brodricyoung/mini-crane-project/Documentation/images/schematics/pinout-L298N-B.png

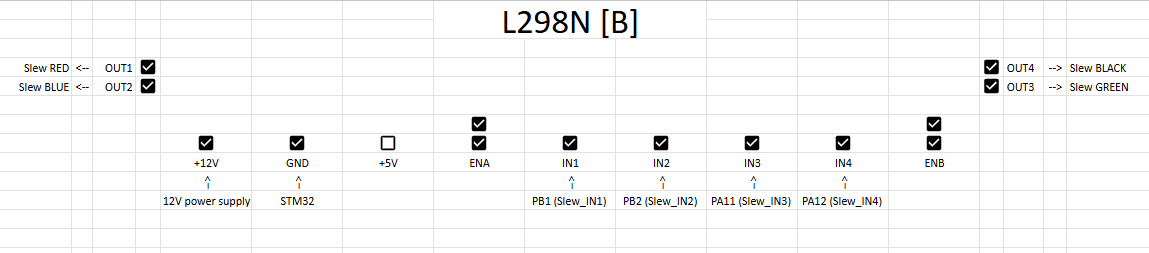
Documentation/images/schematics/pinout-L298N-B.png
