brodricyoung/mini-crane-project/KiCad_files_for_PCB/projects/STM32Nucleo_L476RG_Baseboard/image-of-3d-front-in-KiCad.png

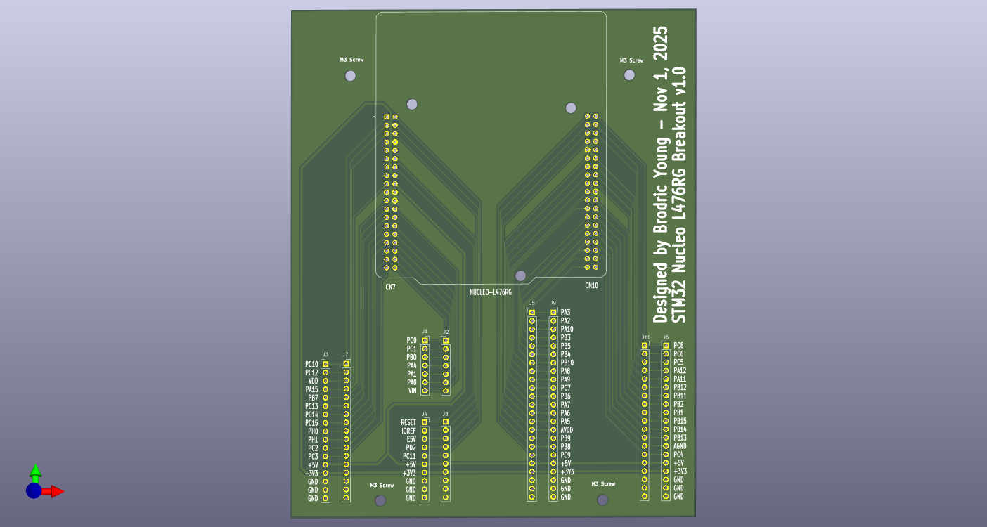
KiCad_files_for_PCB/projects/STM32Nucleo_L476RG_Baseboard/image-of-3d-front-in-KiCad.png
