brodricyoung/mini-crane-project/Documentation/images/components-in-system/pushbuttons-on-controller.JPG

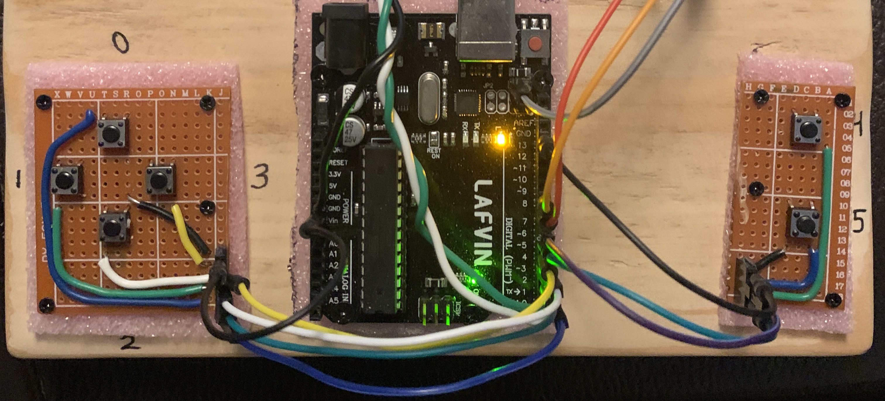
Documentation/images/components-in-system/pushbuttons-on-controller.JPG
