brodricyoung/mini-crane-project/Documentation/images/components-in-system/slew-nema17-stepper-motor.JPG

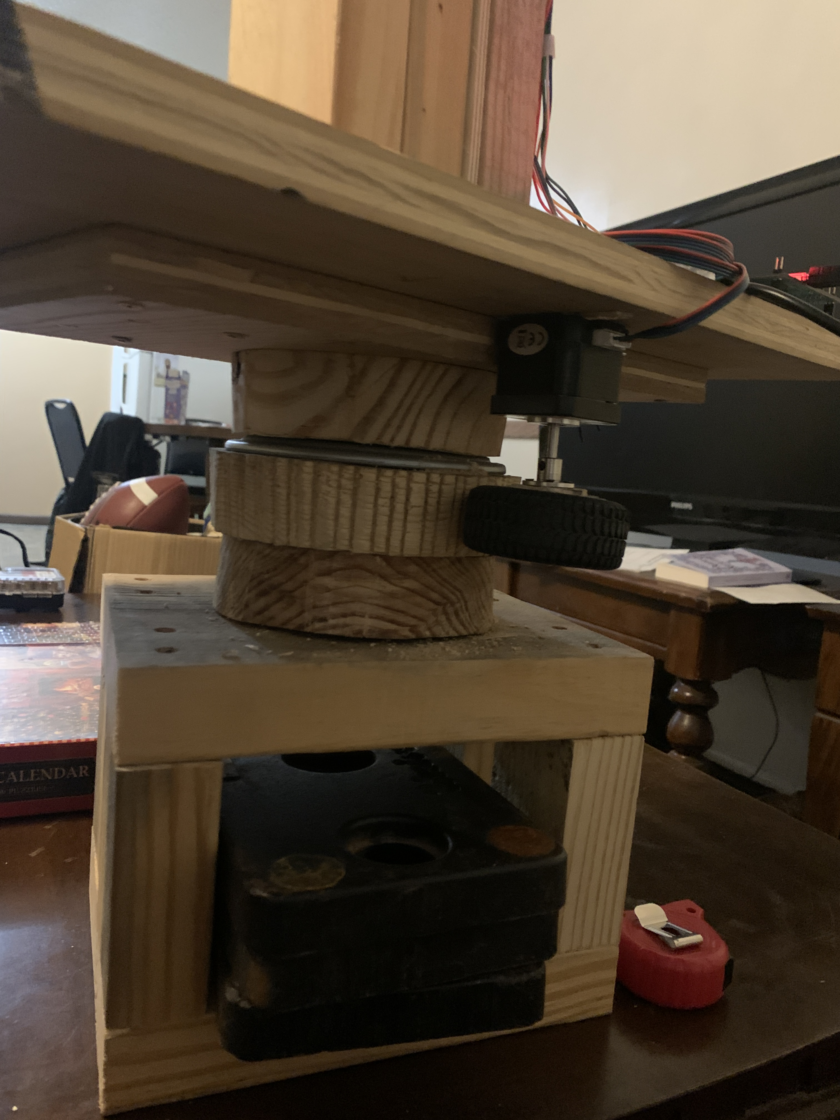
Documentation/images/components-in-system/slew-nema17-stepper-motor.JPG
