brodricyoung/mini-crane-project/Documentation/images/components-in-system/handheld-arduino-controller.JPG

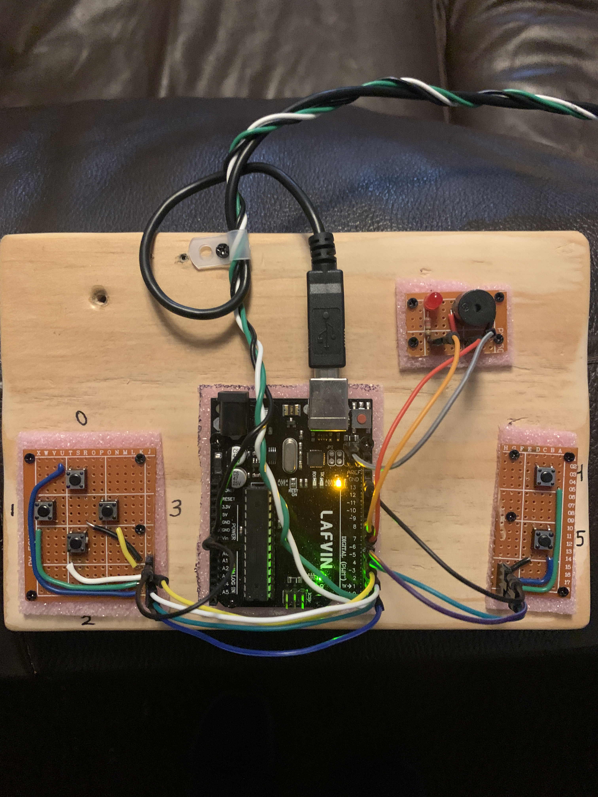
Documentation/images/components-in-system/handheld-arduino-controller.JPG
