brodricyoung/mini-crane-project/Documentation/images/components-in-system/L298N motor drivers.JPG

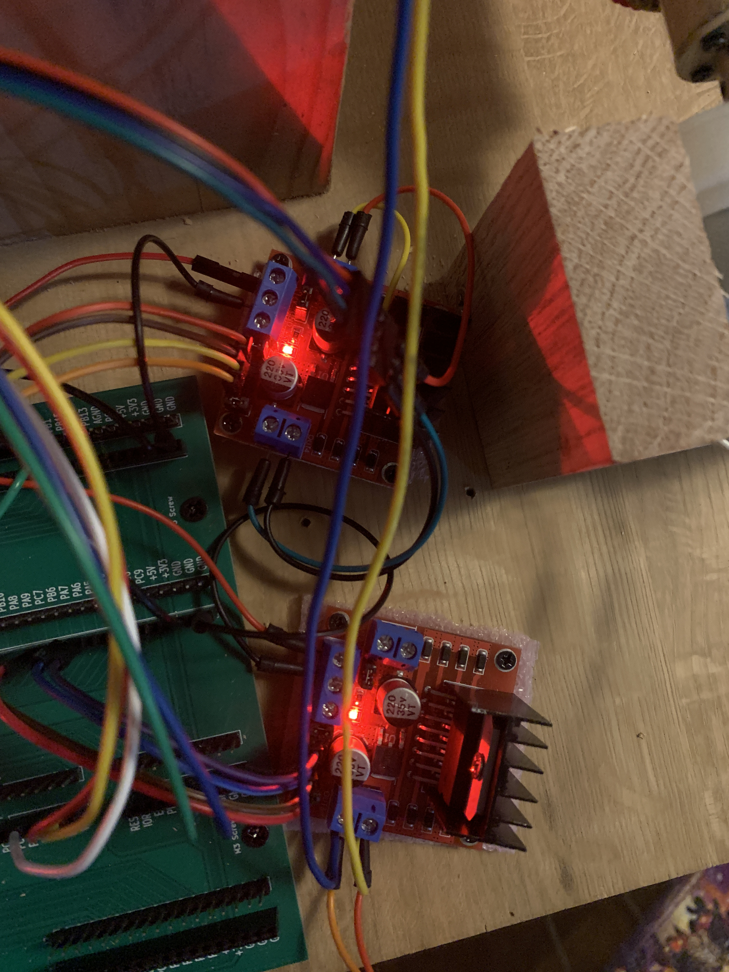
Documentation/images/components-in-system/L298N motor drivers.JPG
