brodricyoung/mini-crane-project/Documentation/images/components-in-system/rotary-encoder.JPG

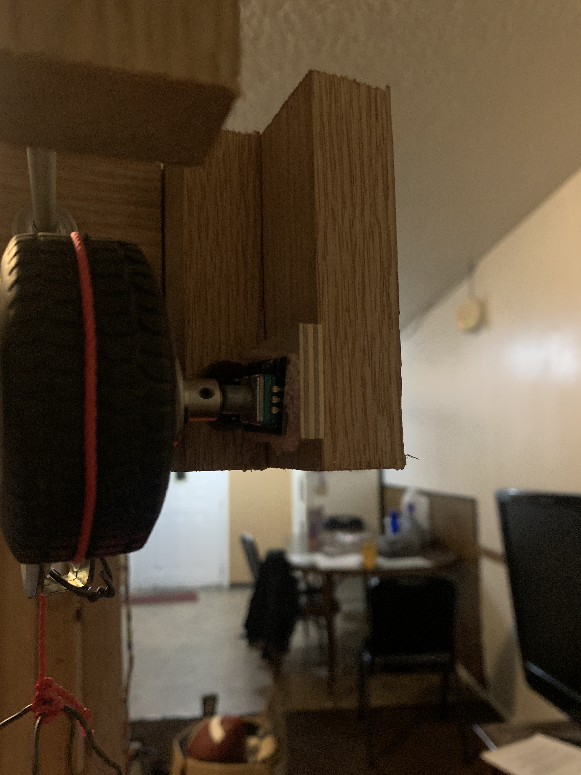
Documentation/images/components-in-system/rotary-encoder.JPG
