brodricyoung/mini-crane-project/Documentation/images/components-in-system/trolley-dc-motor-and-pulley.JPG

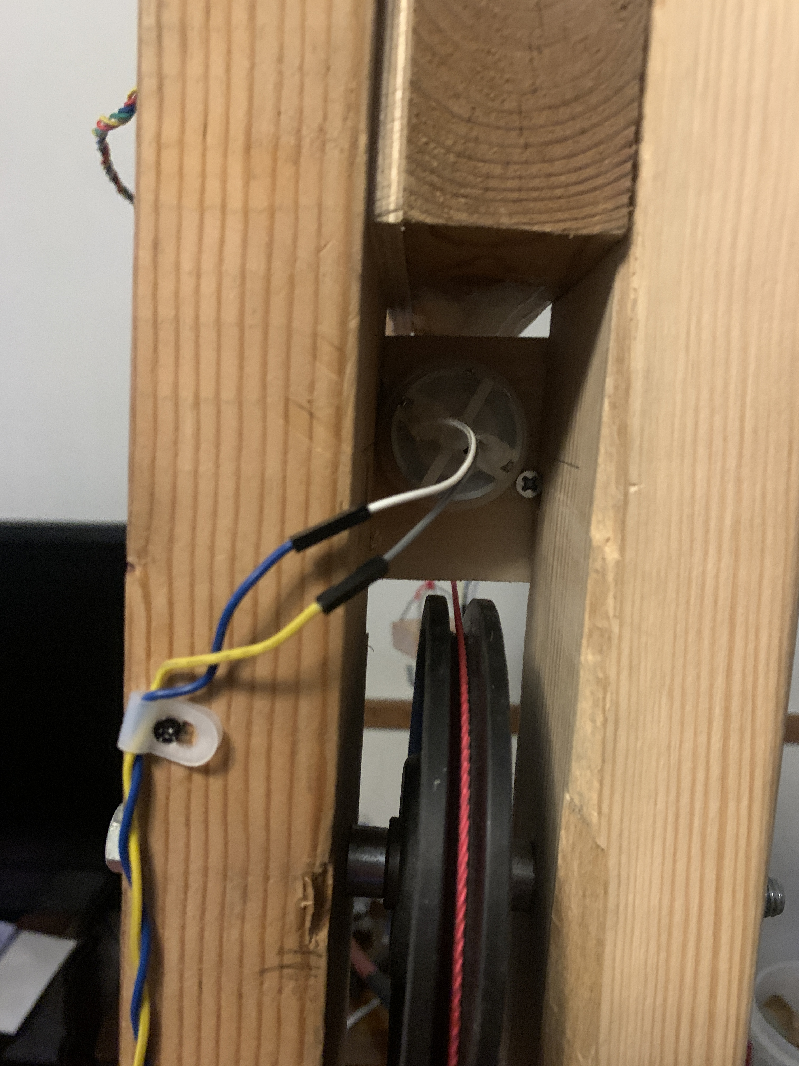
Documentation/images/components-in-system/trolley-dc-motor-and-pulley.JPG
