brodricyoung/mini-crane-project/Documentation/images/components-in-system/winch-dc-motor.JPG

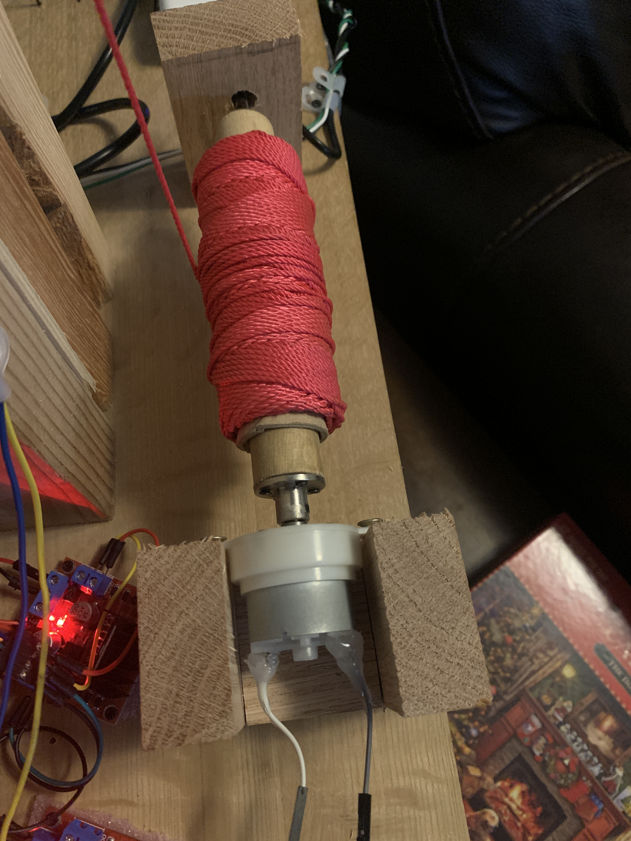
Documentation/images/components-in-system/winch-dc-motor.JPG
